andrewhlu/spl/demo_pics/wireless.png

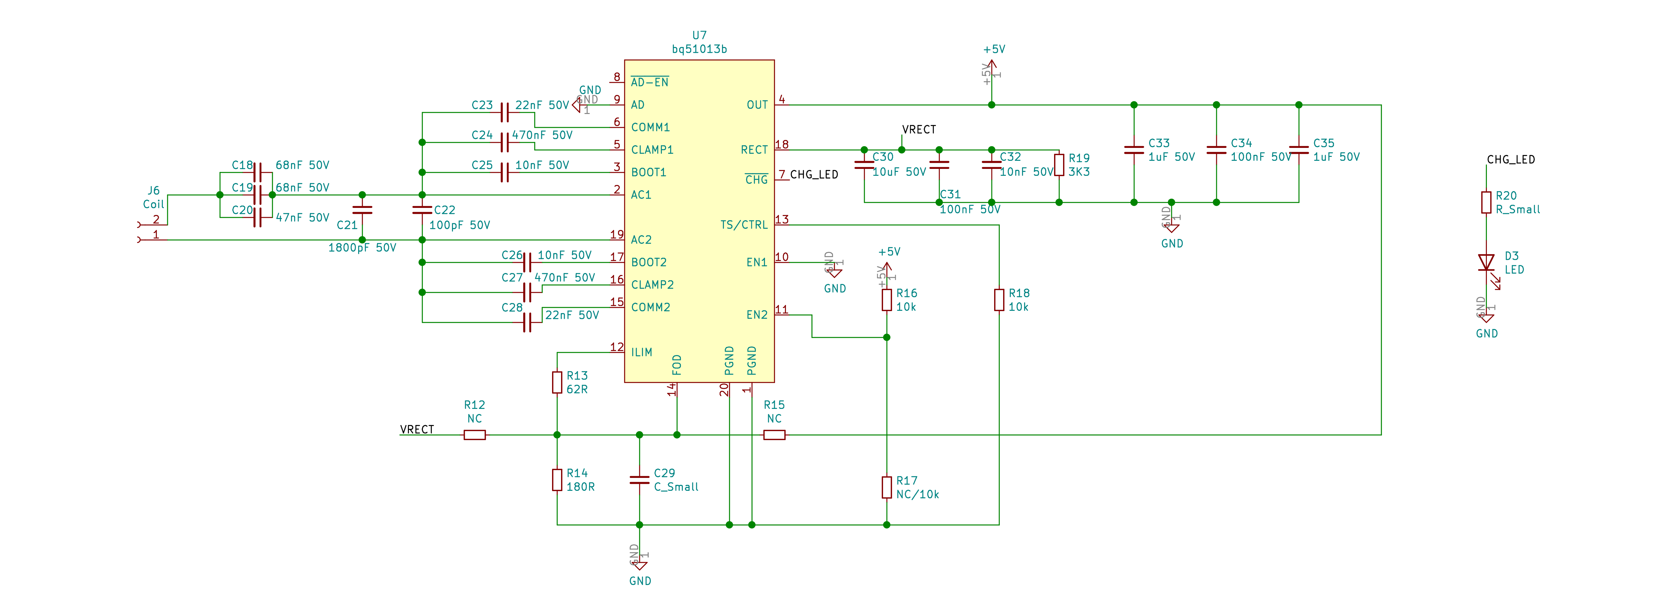
demo_pics/wireless.png
