andrewhlu/spl/demo_pics/PCBAssembly01.png

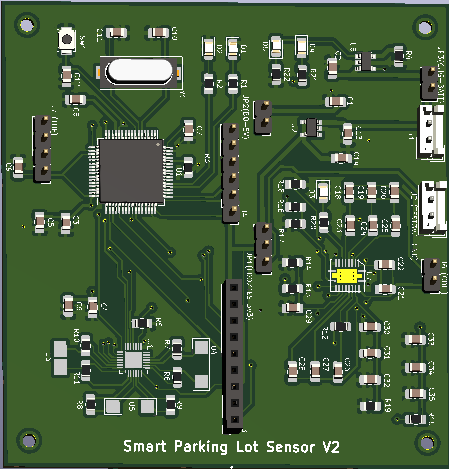
demo_pics/PCBAssembly01.png
